omsi-exhibits/Snow_Melt_Map/docs/Map_LED_Holes.png

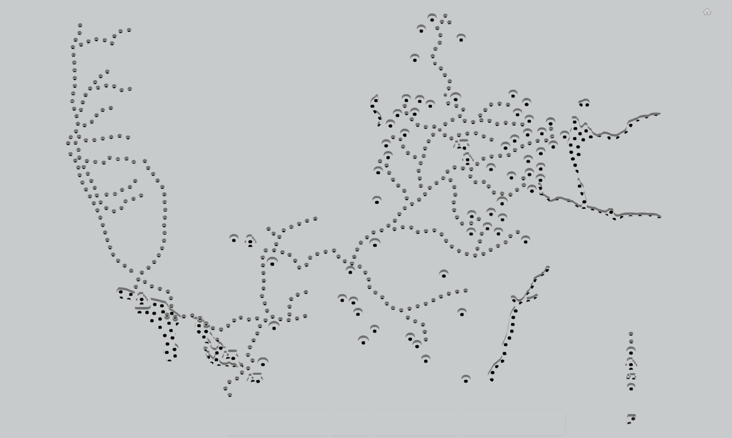
docs/Map_LED_Holes.png
