omsi-exhibits/Snow_Melt_Map/pcb/Bunny_for_silkscreen.bmp

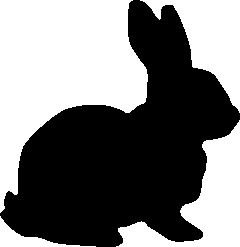
pcb/Bunny_for_silkscreen.bmp
