omsi-exhibits/Snow_Melt_Map/button_controller_arduino/8x_button_io_board_no_keyboard/AudioOut.h

#ifndef AUDIOOUT_H
#define AUDIOOUT_H

#include "wavTrigger.h"

#define AUDIO_TX 
#define AUDIO_RX

class AudioOut {
    public:
        AudioOut();
        void begin();
        void update();
        void playTrack(int trackNum);
        void playTrackSolo(int trackNum);
        void stopAllTracks();
        void randomizePitch();
        void resetPitch();
    private:
        wavTrigger wTrig;

};

#endif
